grappendorf/smarkant/smarkant-kicad/smarkant.sch

## KiCad design smarkant-kicad/smarkant.sch (2017-03-21, an earlier design)

Schematic: smarkant.sch

Parts:
10k1, 10k4, 10k5, 10k7, 10k9: 10k
10k2: 2k2
10k3: 100k
C1, C2: 10µF
C3, C4: 22p
IC1: ATMEGA328P-P; DIL28
LOGO1: OSHW_LOGO_FILL
P1: POW24V
P2: UP
P3: DOWN
P4: ISP
P5: SERIAL1
P6: LINBUS
P7: SERIAL2
Q1: 2N3904; TO-92
SW1: D9
SW2: D10
SW3: D3
SW4: D4
SW5: D5
SW6: D6
U1: RECOMR-783.3-0.5
U2: ESP-12E
Y1: 16MHz
